mduda4742/LineFollower/Firmware/Core/Inc/pid.h

#ifndef PID_H_
#define PID_H_

#include <stdint.h>

typedef struct {
	int32_t p, i, d;

	int32_t p_max, i_max, d_max;

	int32_t p_min, i_min, d_min;

	uint8_t f;
	int32_t power;

	int32_t sum;
	int32_t e_last;

	int32_t total_max;
	int32_t total_min;

	int32_t control;
	int32_t dt_ms;
} cpid_t;

void pid_init(cpid_t * pid, float p, float i, float d, uint8_t f, int32_t dt_ms);

int32_t pid_calc(cpid_t * pid, int32_t mv, int32_t dv);

int32_t pid_scale(cpid_t * pid, float v);

#endif /* PID_H_ */
